AsicVault/asicvault-hardware/photos/IMG_0304_s25.jpg

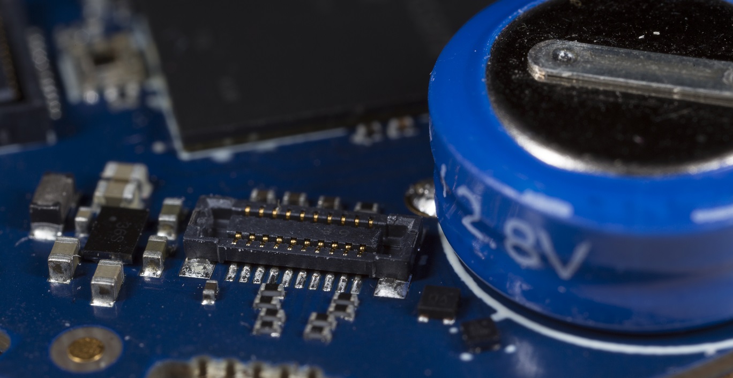
photos/IMG_0304_s25.jpg
