AsicVault/asicvault-hardware/photos/IMG_0316_s25.jpg

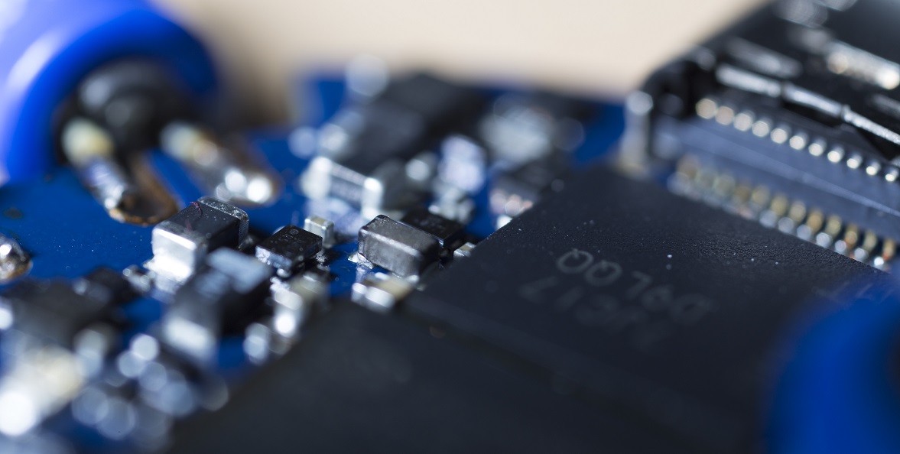
photos/IMG_0316_s25.jpg
