AsicVault/asicvault-hardware/photos/IMG_0320_s25.jpg

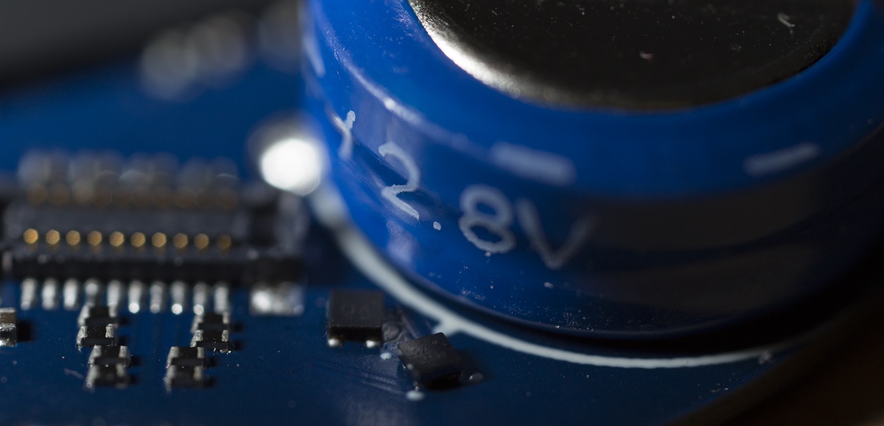
photos/IMG_0320_s25.jpg
