AsicVault/asicvault-hardware/photos/IMG_0322_s25.jpg

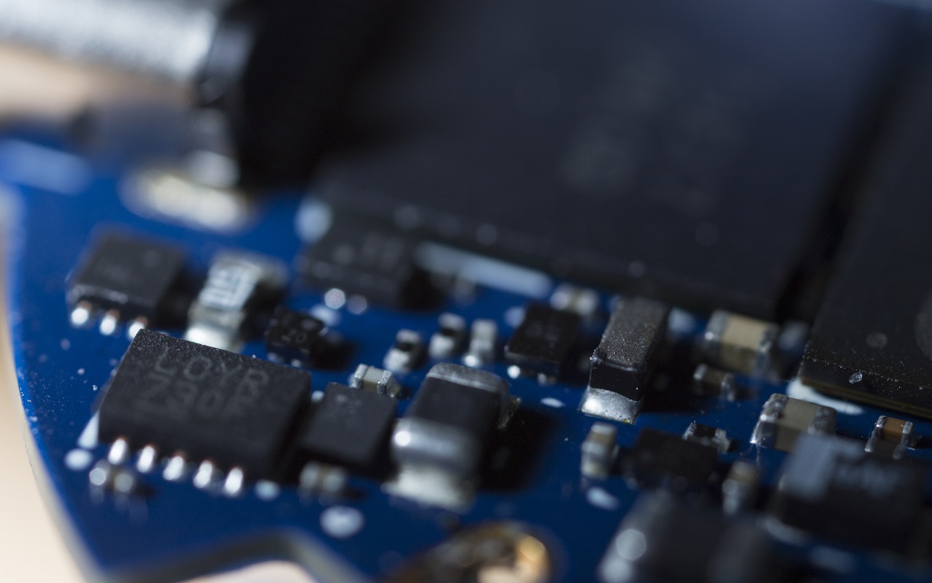
photos/IMG_0322_s25.jpg
