AsicVault/asicvault-hardware/photos/IMG_0324_s25.jpg

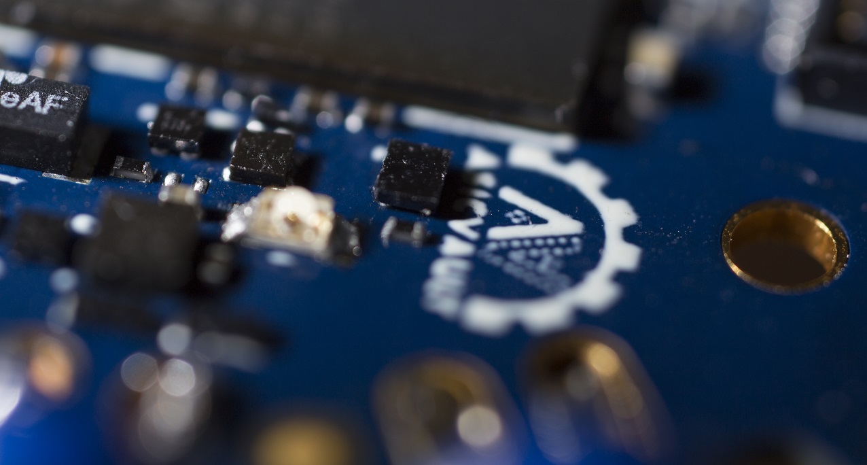
photos/IMG_0324_s25.jpg
