AsicVault/asicvault-hardware/photos/IMG_0335_s25.jpg

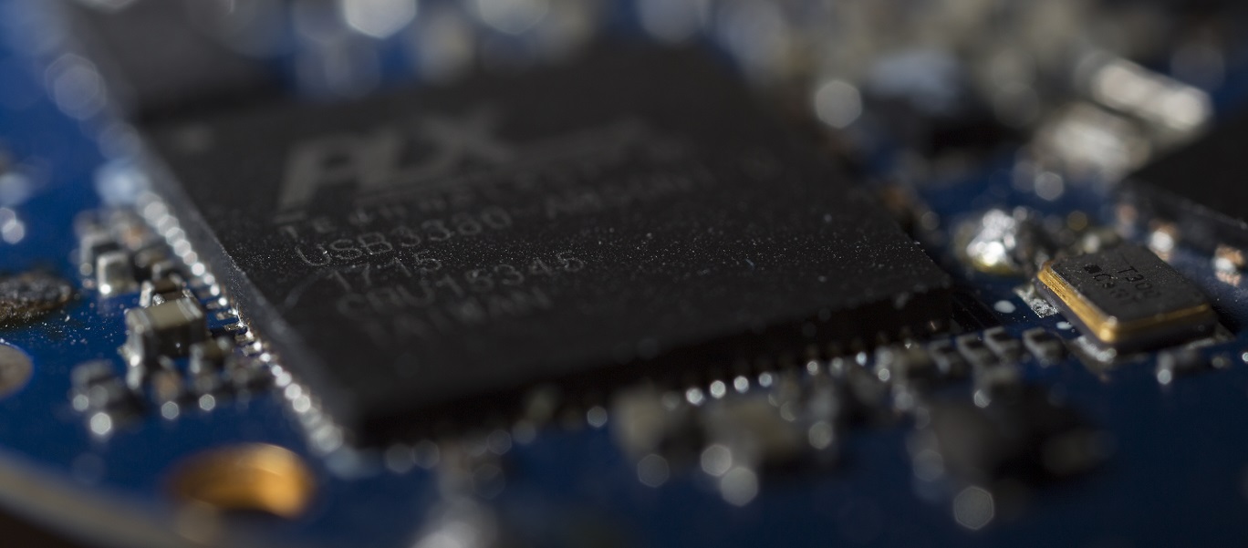
photos/IMG_0335_s25.jpg
