AsicVault/asicvault-hardware/photos/IMG_0338_s25.jpg

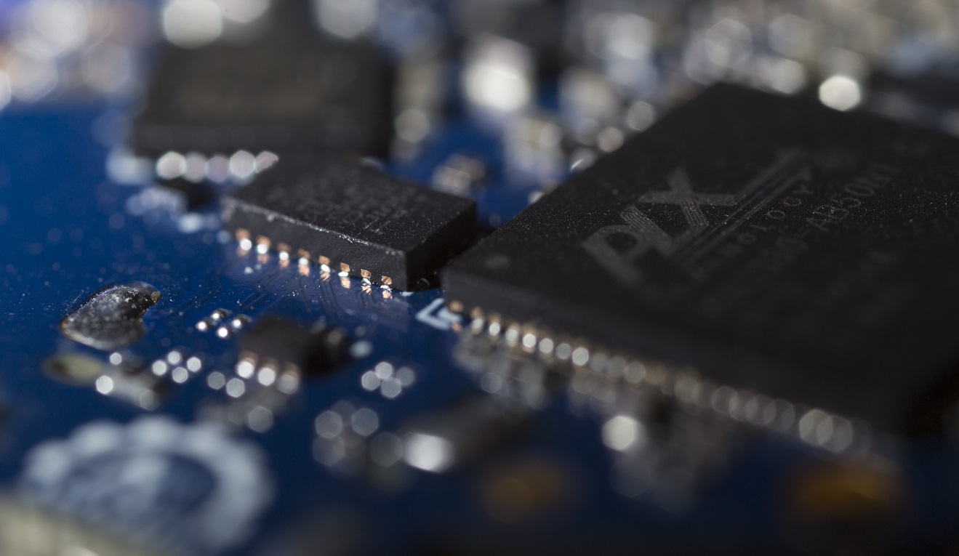
photos/IMG_0338_s25.jpg
