AsicVault/asicvault-hardware/photos/IMG_0339_s25.jpg

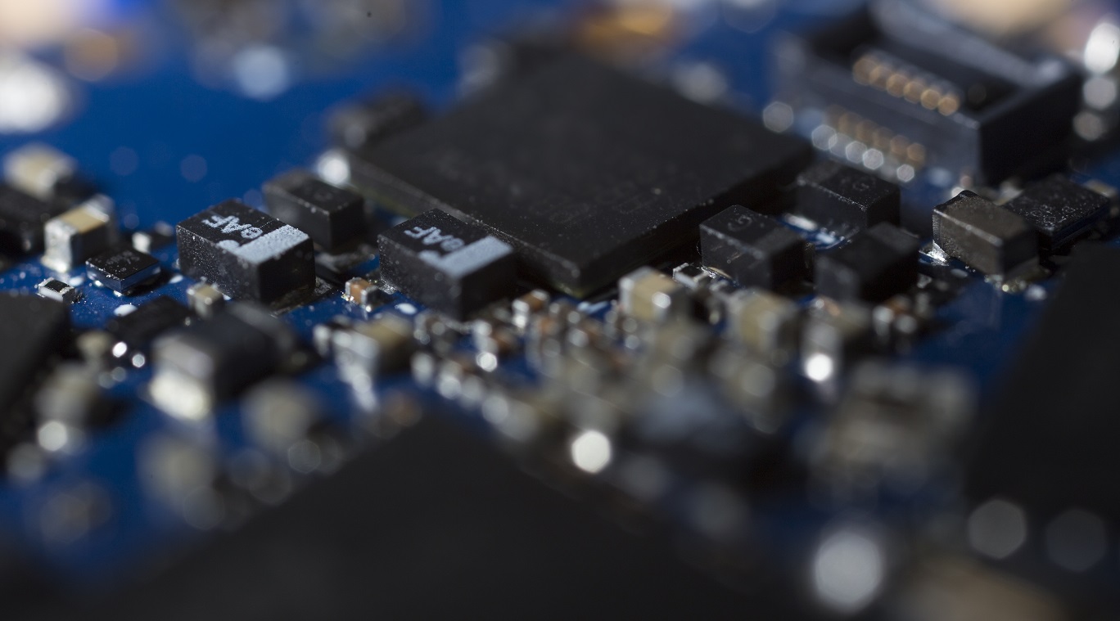
photos/IMG_0339_s25.jpg
