AsicVault/asicvault-hardware/photos/IMG_0342_s25.jpg

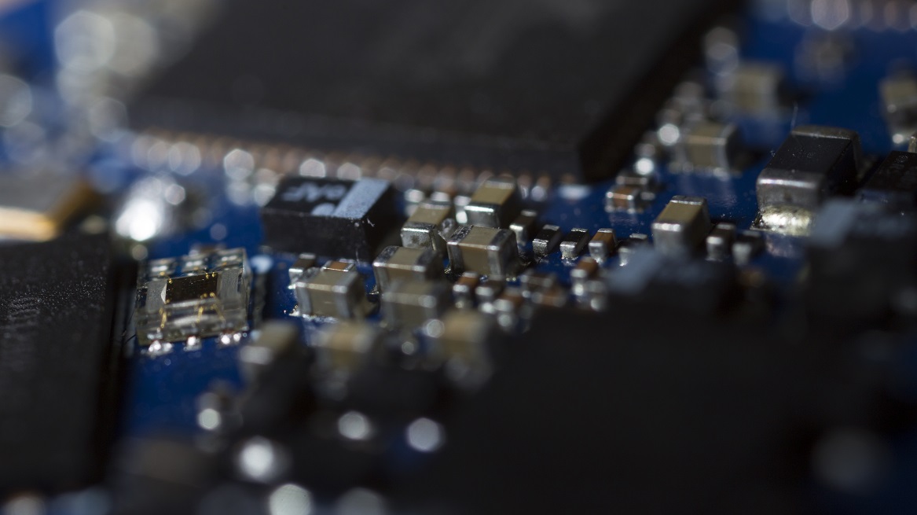
photos/IMG_0342_s25.jpg
