AsicVault/asicvault-hardware/photos/IMG_0394_s25.jpg

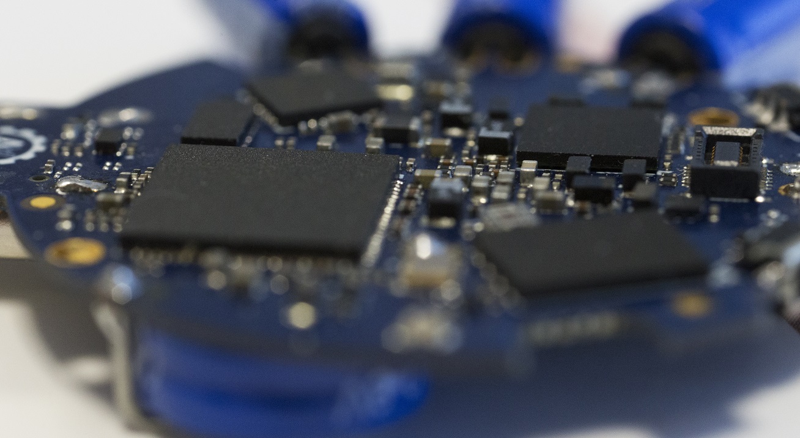
photos/IMG_0394_s25.jpg
