AsicVault/asicvault-hardware/photos/IMG_0404_s25.jpg

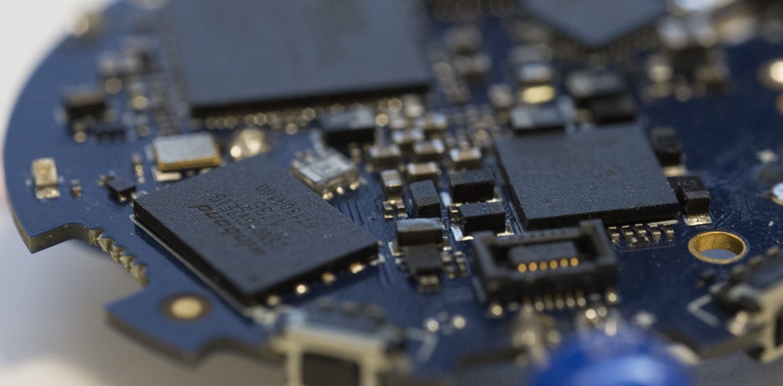
photos/IMG_0404_s25.jpg
