AsicVault/asicvault-hardware/photos/IMG_0514_s25.jpg

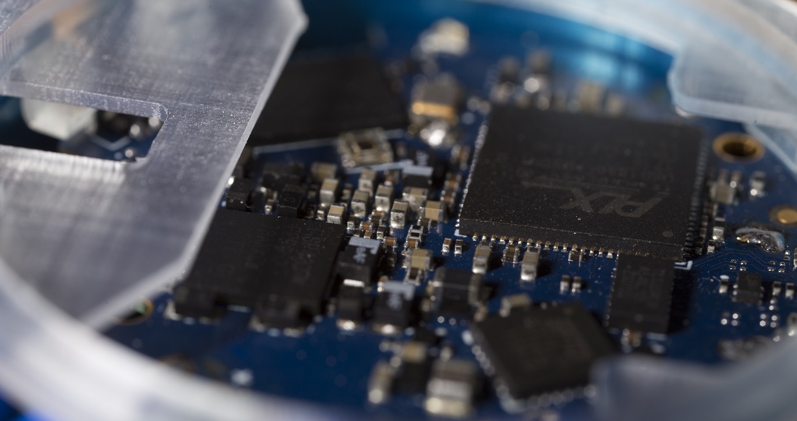
photos/IMG_0514_s25.jpg
