AsicVault/asicvault-hardware/photos/IMG_0517_s25.jpg

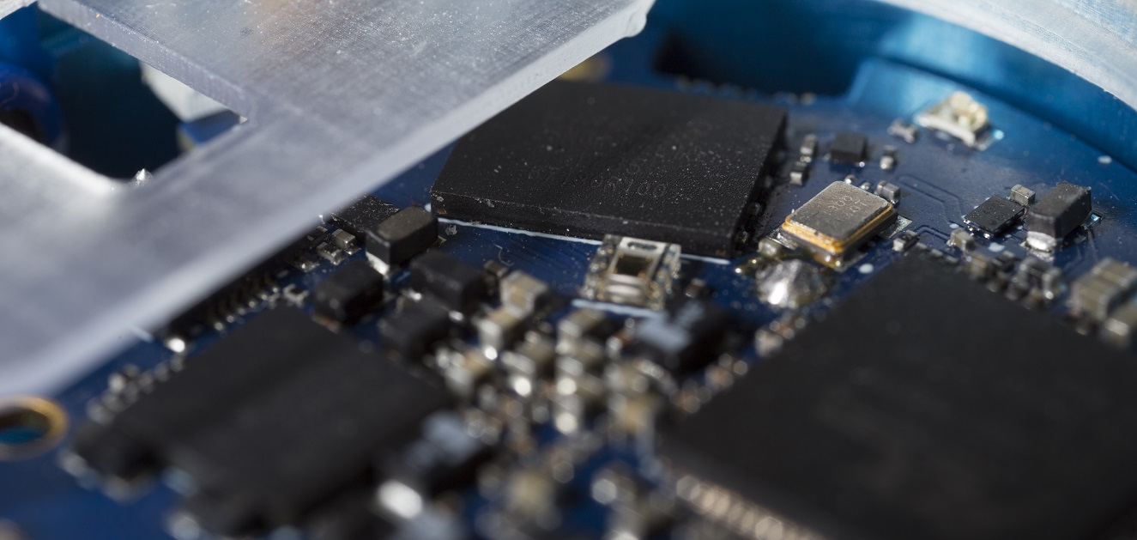
photos/IMG_0517_s25.jpg
